GiuliaTitton/RP_2040/PSE_RP2040/PSE_RP2040.kicad_sch

## KiCad design PSE_RP2040/PSE_RP2040.kicad_sch (2022-04-23)

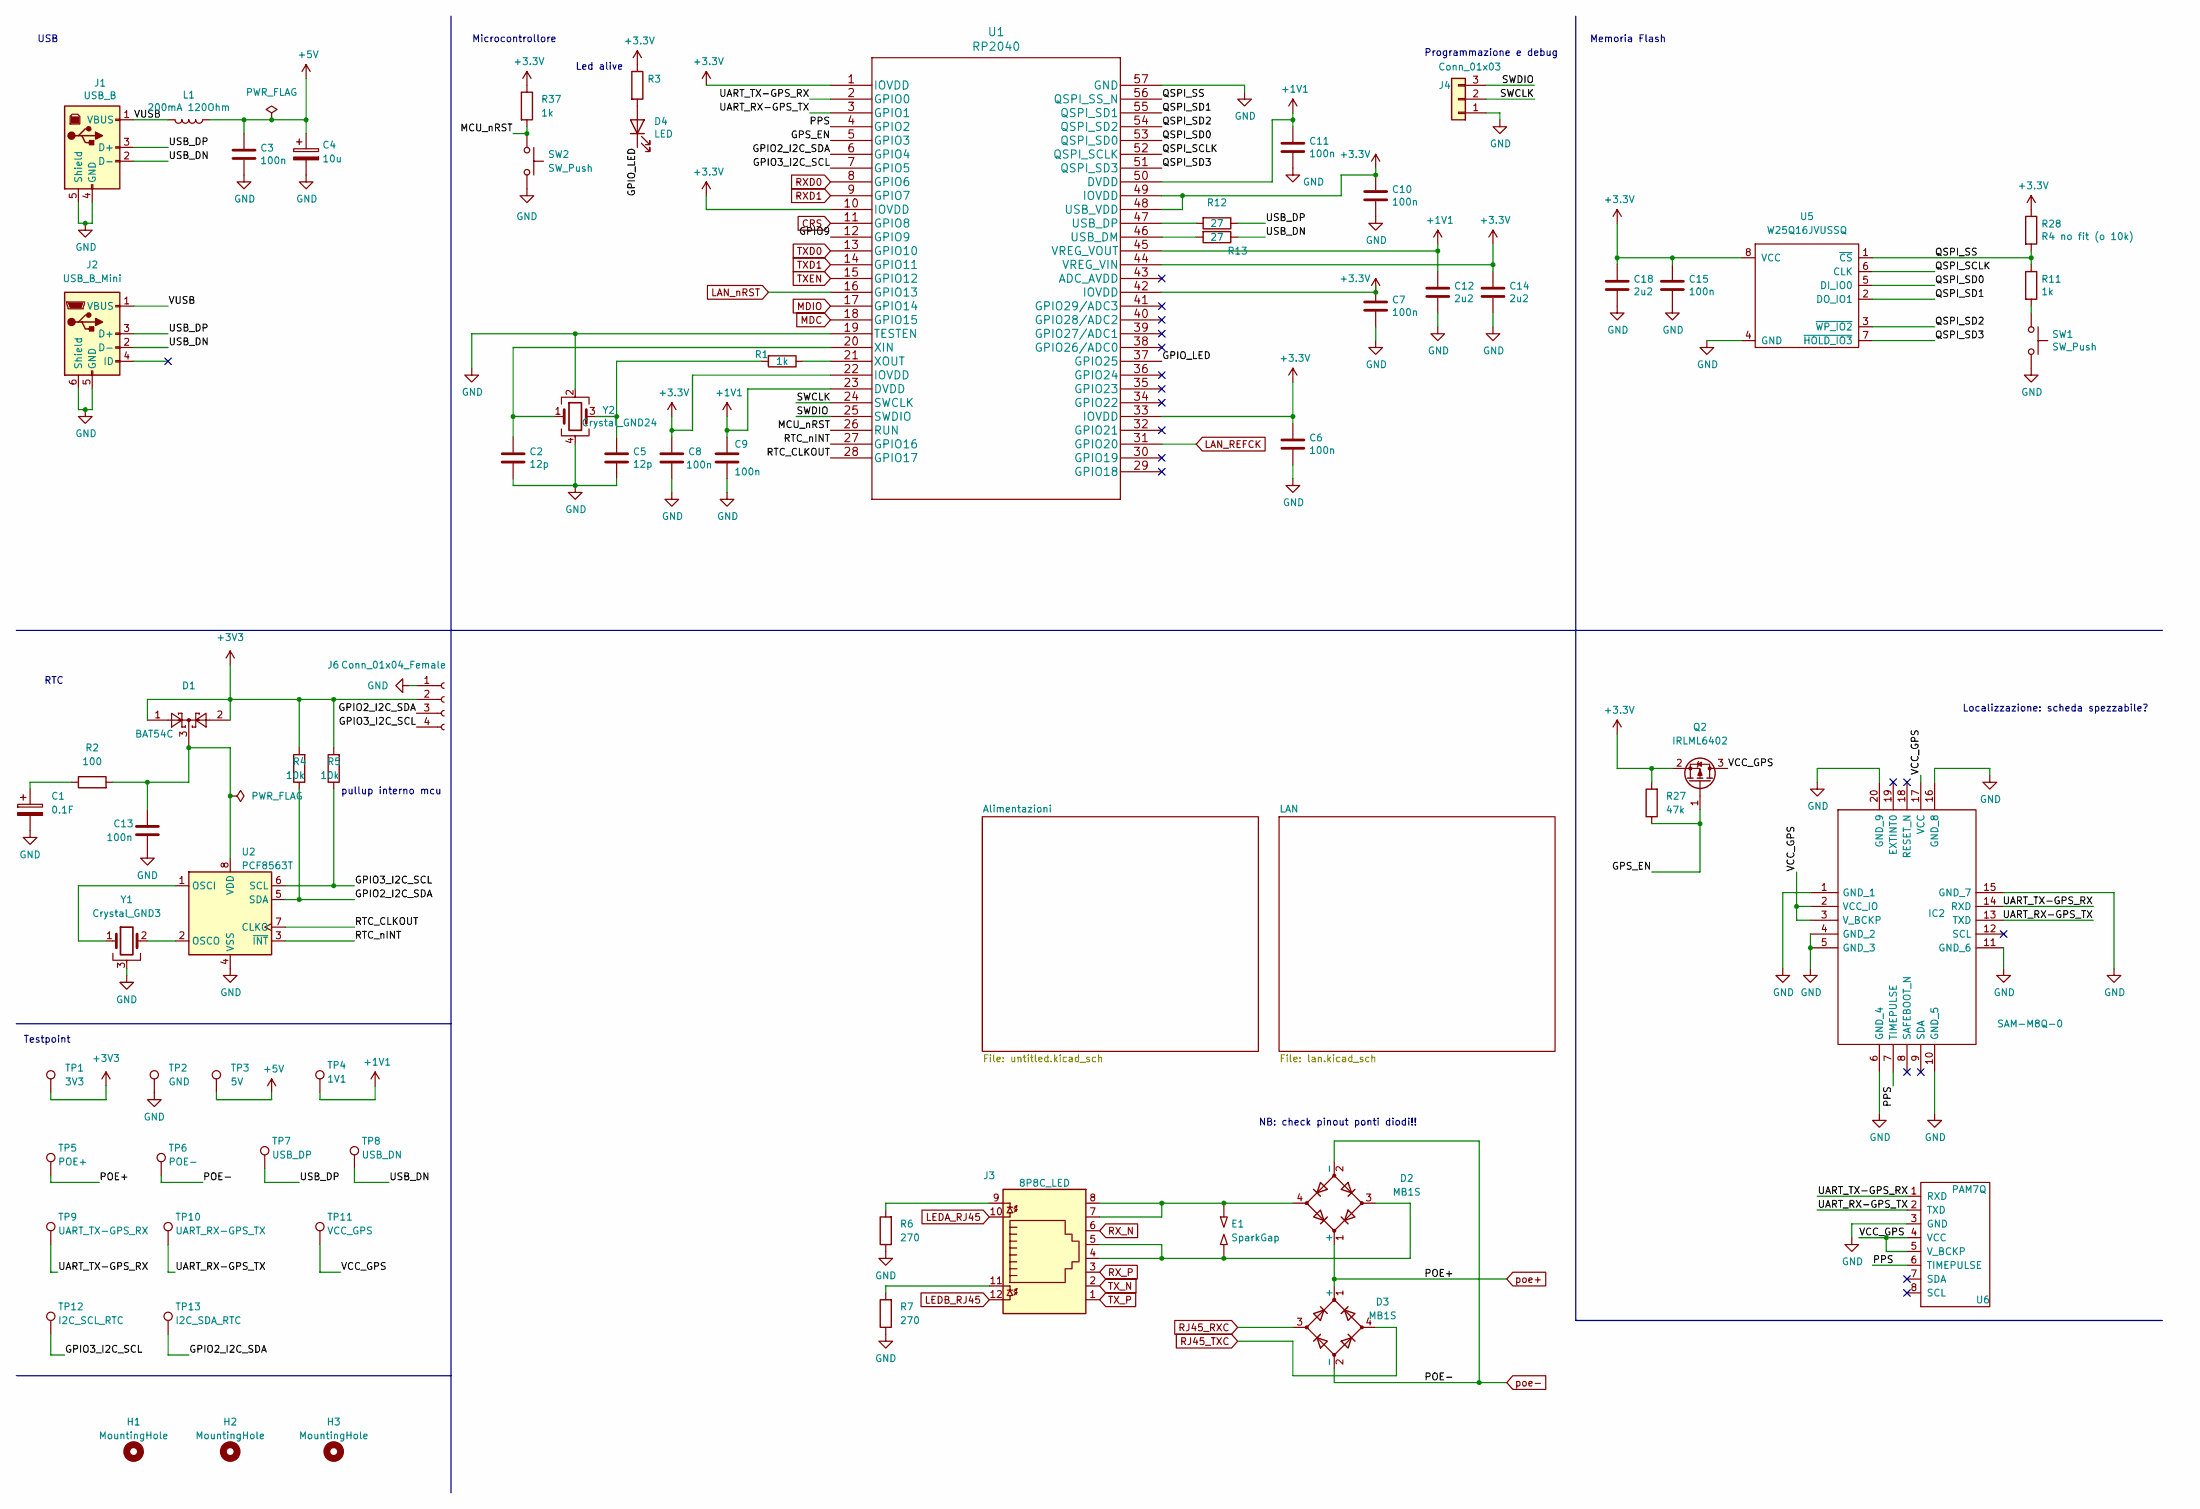
[picture p20: schematic PSE_RP2040.kicad_sch]

Parts:
C1: 0.1F; CP_Radial_D10.0mm_P5.00mm
C2, C5: 12p; C_0603_1608Metric
C3, C6, C7, C8, C9, C10, C11, C13, C15: 100n; C_0603_1608Metric
C4: 10u; C_0805_2012Metric
C12, C14, C18: 2u2; C_0603_1608Metric
D1: BAT54C; SOT-23
D2, D3: MB1S; SO-4_4.4x3.6mm_P2.54mm
D4: LED; LED_0603_1608Metric
E1: SparkGap; SPARK_GAP_TRIANGLE
H1, H2, H3: MountingHole; MountingHole_3mm
IC2: SAM-M8Q-0; SAM-M8Q; Manufacturer_Part_Number SAM-M8Q-0; Mouser Part Number 377-SAM-M8Q-0
J1: USB_B; USB_B_OST_USB-B1HSxx_Horizontal
J2: USB_B_Mini; USB_Mini-B_Wuerth_65100516121_Horizontal
J3: 8P8C_LED; RJ45_Amphenol_RJHSE-5081
J4: Conn_01x03; PinHeader_1x03_P2.54mm_Vertical
J6: Conn_01x04_Female; PinHeader_1x04_P2.54mm_Vertical
L1: 200mA 120Ohm; L_0603_1608Metric
Q2: IRLML6402; SOT-23
R1, R11, R37: 1k; R_0603_1608Metric
R2: 100; R_0603_1608Metric
R3: R_0603_1608Metric
R4, R5: 10k; R_0603_1608Metric
R6, R7: 270; R_0603_1608Metric
R12, R13: 27; R_0603_1608Metric
R27: 47k; R_0603_1608Metric
R28: R4 no fit (o 10k); R_0603_1608Metric
SW1, SW2: SW_Push; SW_PUSH_6mm
TP1: 3V3; TestPoint_Loop_D1.80mm_Drill1.0mm_Beaded
TP2: GND; TestPoint_Loop_D1.80mm_Drill1.0mm_Beaded
TP3: 5V; TestPoint_Pad_D1.0mm
TP4: 1V1; TestPoint_Pad_D1.0mm
TP5: POE+; TestPoint_Pad_D1.0mm
TP6: POE-; TestPoint_Pad_D1.0mm
TP7: USB_DP; TestPoint_Pad_D1.0mm
TP8: USB_DN; TestPoint_Pad_D1.0mm
TP9: UART_TX-GPS_RX; TestPoint_Pad_D1.0mm
TP10: UART_RX-GPS_TX; TestPoint_Pad_D1.0mm
TP11: VCC_GPS; TestPoint_Pad_D1.0mm
TP12: I2C_SCL_RTC; TestPoint_Pad_D1.0mm
TP13: I2C_SDA_RTC; TestPoint_Pad_D1.0mm
U1: RP2040; RP2040-QFN-56
U2: PCF8563T; SOIC-8_3.9x4.9mm_P1.27mm
U5: W25Q16JVUSSQ; SOIC-8_5.275x5.275mm_P1.27mm
U6: PAM7Q; PAM-7Q
Y1: Crystal_GND3; Crystal_AT310_D3.0mm_L10.0mm_Horizontal_1EP_style1
Y2: Crystal_GND24; Crystal_SMD_3225-4Pin_3.2x2.5mm

Connections:
+1V1: C9.1, C11.1, C12.1, TP4.1, U1.23 (DVDD), U1.45 (VREG_VOUT), U1.50 (DVDD)
+3.3V: C6.1, C7.1, C8.1, C10.1, C14.1, C15.1, C18.1, Q2.2 (S), R3.1, R27.2, R28.1, R37.1, U1.1 (IOVDD), U1.10 (IOVDD), U1.22 (IOVDD), U1.33 (IOVDD), U1.42 (IOVDD), U1.44 (VREG_VIN), U1.48 (USB_VDD), U1.49 (IOVDD), U5.8 (VCC)
+3V3: D1.1, D1.2, J6.2, R4.2, R5.2, TP1.1
+5V: C3.1, C4.1, L1.1, TP3.1
CRS: U1.11 (GPIO8)
GND: C1.2, C2.2, C3.2, C4.2, C5.2, C6.2, C7.2, C8.2, C9.2, C10.2, C11.2, C12.2, C13.2, C14.2, C15.2, C18.2, IC2.1 (GND_1), IC2.4 (GND_2), IC2.5 (GND_3), IC2.6 (GND_4), IC2.10 (GND_5), IC2.11 (GND_6), IC2.15 (GND_7), IC2.16 (GND_8), IC2.20 (GND_9), J1.4 (GND), J1.5 (Shield), J2.5 (GND), J2.6 (Shield), J4.1, J6.1, R6.1, R7.1, SW1.2, SW2.2, TP2.1, U1.19 (TESTEN), U1.57 (GND), U2.4 (VSS), U5.4 (GND), U6.3 (GND), Y1.3, Y2.2, Y2.4
GPIO2_I2C_SDA: J6.3, R4.1, TP13.1, U1.6 (GPIO4), U2.5 (SDA)
GPIO3_I2C_SCL: J6.4, R5.1, TP12.1, U1.7 (GPIO5), U2.6 (SCL)
GPIO9: U1.12 (GPIO9)
GPIO_LED: D4.1 (K), U1.37 (GPIO25)
GPS_EN: Q2.1 (G), R27.1, U1.5 (GPIO3)
LAN_REFCK: U1.31 (GPIO20)
LAN_nRST: U1.16 (GPIO13)
LEDA_RJ45: J3.10
LEDB_RJ45: J3.12
MCU_nRST: R37.2, SW2.1, U1.26 (RUN)
MDC: U1.18 (GPIO15)
MDIO: U1.17 (GPIO14)
unnamed: C1.1, R2.1
unnamed: C2.1, U1.20 (XIN), Y2.1
unnamed: C5.1, R1.2, Y2.3
unnamed: C13.1, D1.3, R2.2, U2.8 (VDD)
unnamed: D2.3, E1.1, J3.4, J3.5
unnamed: D2.4, E1.2, J3.7, J3.8
unnamed: D4.2 (A), R3.2
unnamed: J3.9, R6.2
unnamed: J3.11, R7.2
unnamed: R1.1, U1.21 (XOUT)
unnamed: R11.2, SW1.1
unnamed: R12.2, U1.47 (USB_DP)
unnamed: R13.2, U1.46 (USB_DM)
unnamed: U2.1 (OSCI), Y1.1
unnamed: U2.2 (OSCO), Y1.2
PPS: IC2.7 (TIMEPULSE), U1.4 (GPIO2), U6.6 (TIMEPULSE)
QSPI_SCLK: U1.52 (QSPI_SCLK), U5.6 (CLK)
QSPI_SD0: U1.53 (QSPI_SD0), U5.5 (DI_IO0)
QSPI_SD1: U1.55 (QSPI_SD1), U5.2 (DO_IO1)
QSPI_SD2: U1.54 (QSPI_SD2), U5.3 (~WP_IO2)
QSPI_SD3: U1.51 (QSPI_SD3), U5.7 (~HOLD_IO3)
QSPI_SS: R11.1, R28.2, U1.56 (QSPI_SS_N), U5.1 (~CS)
RJ45_RXC: D3.3
RJ45_TXC: D3.4
RTC_CLKOUT: U1.28 (GPIO17), U2.7 (CLKO)
RTC_nINT: U1.27 (GPIO16), U2.3 (~INT)
RXD0: U1.8 (GPIO6)
RXD1: U1.9 (GPIO7)
RX_N: J3.6
RX_P: J3.3
SWCLK: J4.2, U1.24 (SWCLK)
SWDIO: J4.3, U1.25 (SWDIO)
TXD0: U1.13 (GPIO10)
TXD1: U1.14 (GPIO11)
TXEN: U1.15 (GPIO12)
TX_N: J3.2
TX_P: J3.1
UART_RX-GPS_TX: IC2.13 (TXD), TP10.1, U1.3 (GPIO1), U6.2 (TXD)
UART_TX-GPS_RX: IC2.14 (RXD), TP9.1, U1.2 (GPIO0), U6.1 (RXD)
USB_DN: J1.2 (D-), J2.2 (D-), R13.1, TP8.1
USB_DP: J1.3 (D+), J2.3 (D+), R12.1, TP7.1
VCC_GPS: IC2.2 (VCC_IO), IC2.3 (V_BCKP), IC2.17 (VCC), Q2.3 (D), TP11.1, U6.4 (VCC), U6.5 (V_BCKP)
VUSB: J1.1 (VBUS), J2.1 (VBUS), L1.2
poe+: D2.1 (+), D3.1 (+), TP5.1
poe-: D2.2 (-), D3.2 (-), TP6.1

Notes on the sheet:
Memoria Flash
USB
pullup interno mcu
RTC
Led alive
Programmazione e debug
Testpoint
NB: check pinout ponti diodi!!
Localizzazione: scheda spezzabile?
Microcontrollore
