GiuliaTitton/RP_2040/PSE_RP2040/lan.kicad_sch

## KiCad design PSE_RP2040/lan.kicad_sch (2022-04-23)

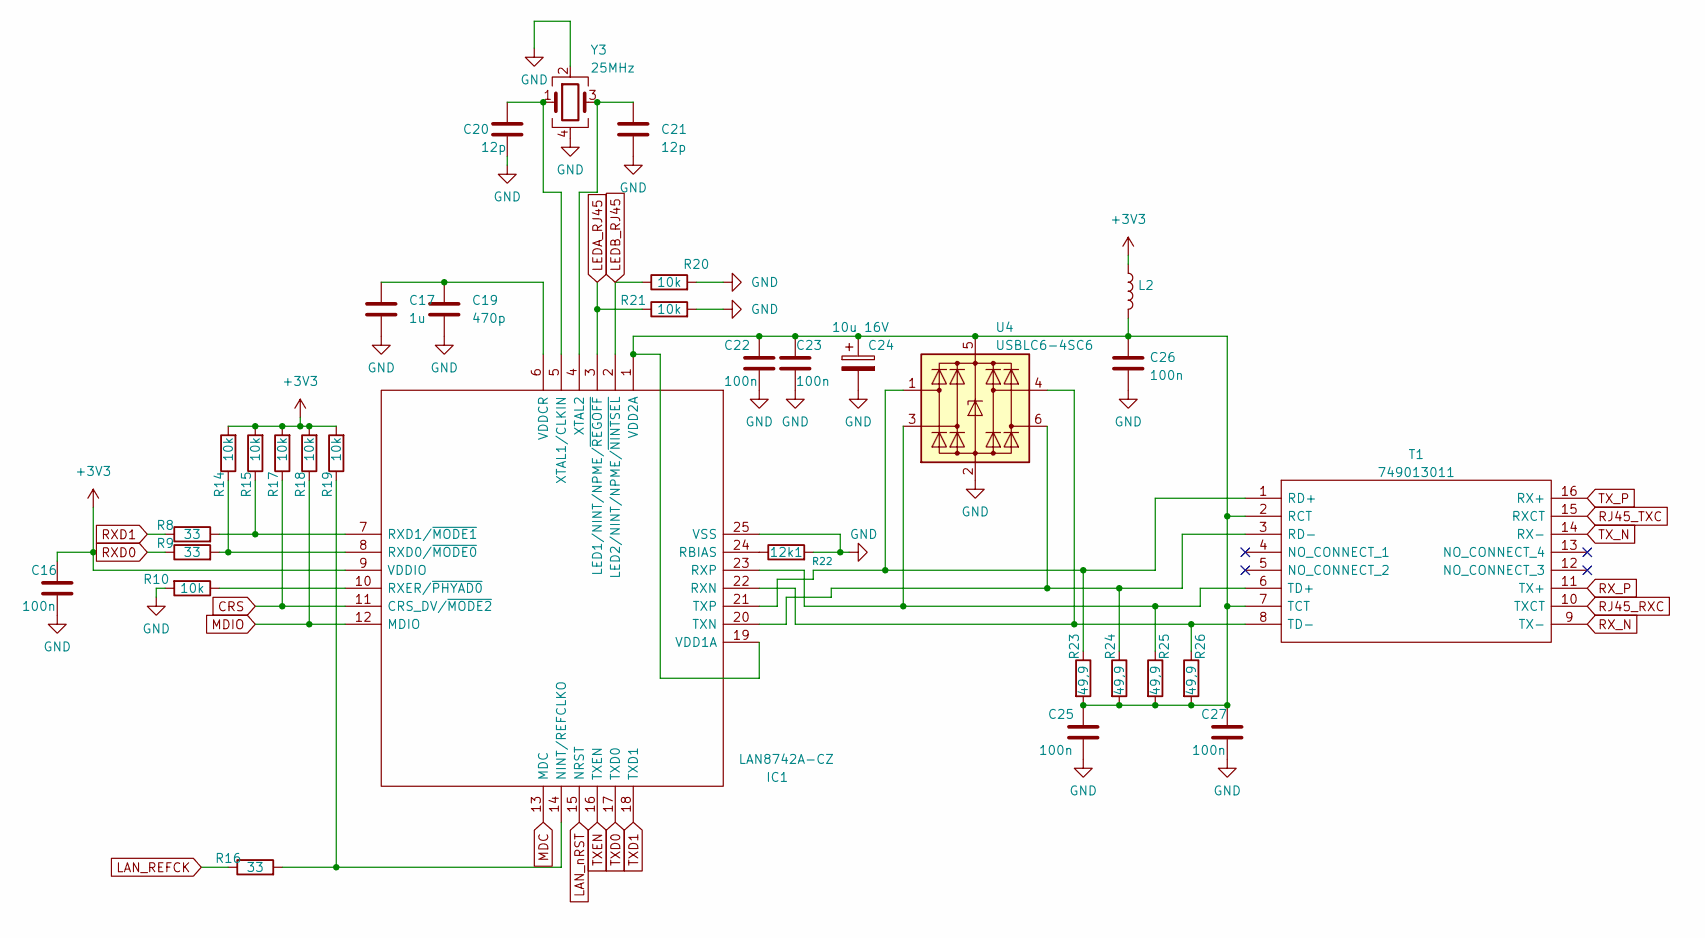
[picture p21: schematic lan.kicad_sch]

Parts:
C16, C22, C23, C25, C26, C27: 100n; C_0603_1608Metric
C17: 1u; C_0603_1608Metric
C19: 470p; C_0603_1608Metric
C20, C21: 12p; C_0603_1608Metric
C24: 10u 16V; C_0805_2012Metric
IC1: LAN8742A-CZ; HVQFN-24-1EP_4x4mm_P0.5mm_EP2.5x2.5mm_ThermalVias; Mouser Part Number 579-LAN8742A-CZ
L2: L_0603_1608Metric
R8, R9, R16: 33; R_0603_1608Metric
R10, R14, R15, R17, R18, R19, R20, R21: 10k; R_0603_1608Metric
R22: 12k1; R_0603_1608Metric
R23, R24, R25, R26: 49,9; R_0603_1608Metric
T1: 749013011; Transformer_Ethernet_Wuerth_749013011A; Mouser Part Number 710-749013011
U4: USBLC6-4SC6; SOT-23-6
Y3: 25MHz; Crystal_SMD_3225-4Pin_3.2x2.5mm

Connections:
+3V3: C16.1, IC1.9 (VDDIO), L2.1, R14.2, R15.2, R17.2, R18.2, R19.2
CRS: IC1.11 (CRS_DV/~MODE2), R17.1
GND: C16.2, C17.2, C19.2, C20.2, C21.2, C22.2, C23.2, C24.2, C25.2, C26.2, C27.2, IC1.25 (VSS), R10.2, R20.2, R21.2, R22.2, U4.2 (GND), Y3.2, Y3.4
LAN_REFCK: R16.1
LAN_nRST: IC1.15 (NRST)
LEDA_RJ45: IC1.3 (LED1/NINT/NPME/~REGOFF), R21.1
LEDB_RJ45: IC1.2 (LED2/NINT/NPME/~NINTSEL), R20.1
MDC: IC1.13 (MDC)
MDIO: IC1.12 (MDIO), R18.1
unnamed: C17.1, C19.1, IC1.6 (VDDCR)
unnamed: C20.1, IC1.5 (XTAL1/CLKIN), Y3.1
unnamed: C21.1, IC1.4 (XTAL2), Y3.3
unnamed: C22.1, C23.1, C24.1, C25.1, C26.1, C27.1, IC1.1 (VDD2A), IC1.19 (VDD1A), L2.2, R23.2, R24.2, R25.2, R26.2, T1.2 (RCT), T1.7 (TCT), U4.5 (VBUS)
unnamed: IC1.7 (RXD1/~MODE1), R8.2, R15.1
unnamed: IC1.8 (RXD0/~MODE0), R9.2, R14.1
unnamed: IC1.10 (RXER/~PHYAD0), R10.1
unnamed: IC1.14 (NINT/REFCLKO), R16.2, R19.1
unnamed: IC1.20 (TXN), R24.1, T1.3 (RD-), U4.6 (I/O4)
unnamed: IC1.21 (TXP), R23.1, T1.1 (RD+), U4.1 (I/O1)
unnamed: IC1.22 (RXN), R26.1, T1.8 (TD-), U4.4 (I/O3)
unnamed: IC1.23 (RXP), R25.1, T1.6 (TD+), U4.3 (I/O2)
unnamed: IC1.24 (RBIAS), R22.1
RJ45_RXC: T1.10 (TXCT)
RJ45_TXC: T1.15 (RXCT)
RXD0: R9.1
RXD1: R8.1
RX_N: T1.9 (TX-)
RX_P: T1.11 (TX+)
TXD0: IC1.17 (TXD0)
TXD1: IC1.18 (TXD1)
TXEN: IC1.16 (TXEN)
TX_N: T1.14 (RX-)
TX_P: T1.16 (RX+)
