GiuliaTitton/RP_2040/PSE_RP2040/untitled.kicad_sch

## KiCad design PSE_RP2040/untitled.kicad_sch (2022-04-12)

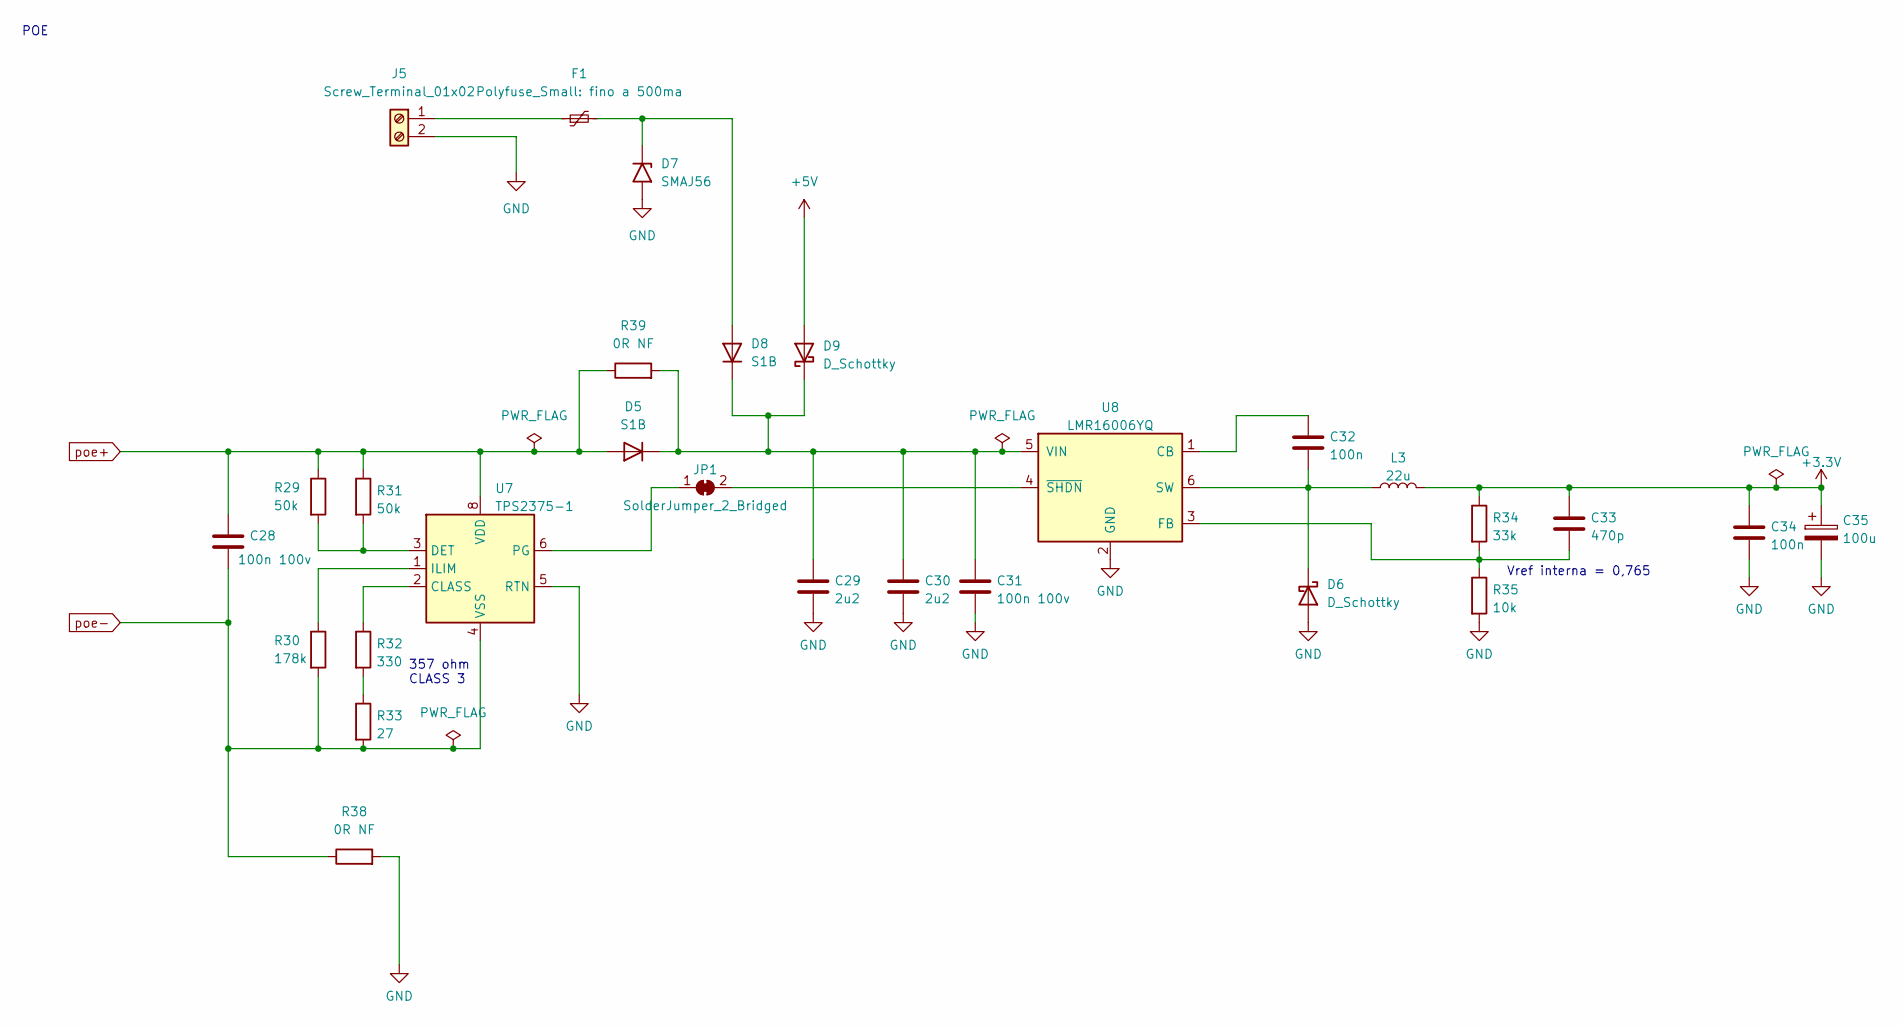
[picture p22: schematic untitled.kicad_sch]

Parts:
C28, C31: 100n 100v; C_0603_1608Metric
C29, C30: 2u2; C_0603_1608Metric
C32, C34: 100n; C_0603_1608Metric
C33: 470p; C_0603_1608Metric
C35: 100u; C_0805_2012Metric
D5, D8: S1B; D_SMA
D6, D9: D_Schottky; D_SMA
D7: SMAJ56; D_SMA
F1: Polyfuse_Small: fino a 500ma; Fuse_1812_4532Metric
J5: Screw_Terminal_01x02; TerminalBlock_Phoenix_MKDS-1,5-2-5.08_1x02_P5.08mm_Horizont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
JP1: SolderJumper_2_Bridged; SolderJumper-2_P1.3mm_Bridged_Pad1.0x1.5mm
L3: 22u; L_Vishay_IFSC-1515AH_4x4x1.8mm
R29, R31: 50k; R_0603_1608Metric
R30: 178k; R_0603_1608Metric
R32: 330; R_0603_1608Metric
R33: 27; R_0603_1608Metric
R34: 33k; R_0603_1608Metric
R35: 10k; R_0603_1608Metric
R38, R39: 0R NF; R_0603_1608Metric
U7: TPS2375-1; SOIC-8_5.275x5.275mm_P1.27mm
U8: LMR16006YQ; SOT-23-6

Connections:
+3.3V: C33.1, C34.1, C35.1, L3.2, R34.1
+5V: D9.2 (A)
GND: C29.2, C30.2, C31.2, C34.2, C35.2, D6.2 (A), D7.2 (A2), J5.2, R35.2, R38.2, U7.5 (RTN), U8.2 (GND)
unnamed: C29.1, C30.1, C31.1, D5.1 (K), D8.1 (K), D9.1 (K), R39.2, U8.5 (VIN)
unnamed: C32.1, U8.1 (CB)
unnamed: C32.2, D6.1 (K), L3.1, U8.6 (SW)
unnamed: C33.2, R34.2, R35.1, U8.3 (FB)
unnamed: D7.1 (A1), D8.2 (A), F1.2
unnamed: F1.1, J5.1
unnamed: JP1.1 (A), U7.6 (PG)
unnamed: JP1.2 (B), U8.4 (~SHDN)
unnamed: R29.2, R31.2, U7.3 (DET)
unnamed: R30.1, U7.1 (ILIM)
unnamed: R32.1, U7.2 (CLASS)
unnamed: R32.2, R33.1
poe+: C28.1, D5.2 (A), R29.1, R31.1, R39.1, U7.8 (VDD)
poe-: C28.2, R30.2, R33.2, R38.1, U7.4 (VSS)

Notes on the sheet:
Vref interna = 0,765
POE
357 ohm CLASS 3
